arrys/OT-Thing/Firmware/src/otvalues.cpp

#include <Arduino.h>
#include "otvalues.h"
#include "otcontrol.h"
#include "mqtt.h"
#include "sensors.h"
#include "devstatus.h"

struct OTItem {
    OpenThermMessageID id;
    PGM_P name;
    static PGM_P getName(OpenThermMessageID id);
};

using enum OpenThermMessageID;

OTValueStatus* OTValue::status = nullptr;
OTValueSlaveConfigMember* OTValue::slaveConfig = nullptr;
OTValueVentSlaveConfigMember* OTValue::ventSlaveConfig = nullptr;

PGM_P KEY_MEMBERID PROGMEM = "memberId";

static const OTItem OTITEMS[] PROGMEM = {
//  ID of message                                   string id for MQTT                  
    {Status,                    PSTR("status")},
    {TSet,                      PSTR("ch_set_t")},
    {MConfigMMemberIDcode,      PSTR("master_config_member")},
    {SConfigSMemberIDcode,      PSTR("slave_config_member")},
    {RemoteRequest,             PSTR("remote_req")},
    {ASFflags,                  PSTR("fault_flags")},
    {RBPflags,                  PSTR("rp_flags")},
    {CoolingControl,            PSTR("cooling_ctrl")},
    {TsetCH2,                   PSTR("ch_set_t2")},
    {TrOverride,                PSTR("tr_override")},
    {TSP,                       PSTR("num_tsps")},
    {FHBsize,                   PSTR("size_fhb")},
    {MaxRelModLevelSetting,     PSTR("max_rel_mod")},
    {MaxCapacityMinModLevel,    PSTR("max_cap_min_mod")},
    {TrSet,                     PSTR("room_set_t")},
    {RelModLevel,               PSTR("rel_mod")},
    {CHPressure,                PSTR("ch_pressure")},
    {DHWFlowRate,               PSTR("dhw_flow_rate")},
    {DayTime,                   PSTR("day_time")},
    {Date,                      PSTR("date")},
    {Year,                      PSTR("year")},
    {TrSetCH2,                  PSTR("room_set_t2")},
    {Tr,                        PSTR("room_t")},
    {Tboiler,                   PSTR("flow_t")},
    {Tdhw,                      PSTR("dhw_t")},
    {Toutside,                  PSTR("outside_t")},
    {Tret,                      PSTR("return_t")},
    {TflowCH2,                  PSTR("flow_t2")},
    {Tdhw2,                     PSTR("dhw_t2")},
    {Texhaust,                  PSTR("exhaust_t")},
    {TboilerHeatExchanger,      PSTR("boiler_heat_ex_t")},
    {BoilerFanSpeedSetpointAndActual, PSTR("boiler_fan")},
    {FlameCurrent,              PSTR("flame_current")},
    {TrCH2,                     PSTR("room_t2")},
    {TrOverride2,               PSTR("tr_override2")},           
    {TdhwSetUBTdhwSetLB,        PSTR("dhw_bounds")},
    {MaxTSetUBMaxTSetLB,        PSTR("ch_bounds")},
    {TdhwSet,                   PSTR("dhw_set_t")},
    {MaxTSet,                   PSTR("max_set_t")},
    {StatusVentilationHeatRecovery, PSTR("vent_status")},
    {Vset,                      PSTR("rel_vent_set")},
    {ASFflagsOEMfaultCodeVentilationHeatRecovery, PSTR("vent_fault_flags")},
    {SConfigSMemberIDCodeVentilationHeatRecovery, PSTR("vent_slave_config_member")},
    {OpenThermVersionVentilationHeatRecovery,   PSTR("vent_ot_version")},
    {VentilationHeatRecoveryVersion,    PSTR("vent_prod_version")},
    {RelVentLevel,              PSTR("rel_vent")},
    {RHexhaust,                 PSTR("rel_hum_exhaust")},
    {CO2exhaust,                PSTR("co2_exhaust")},
    {Tsi,                       PSTR("supply_inlet_t")},
    {Tso,                       PSTR("supply_outlet_t")},
    {Tei,                       PSTR("exhaust_inlet_t")},
    {Teo,                       PSTR("exhaust_outlet_t")},
    {RPMexhaust,                PSTR("exhaust_fan_speed")},
    {RPMsupply,                 PSTR("supply_fan_speed")},
    {Brand,                     PSTR("brand")},
    {BrandVersion,              PSTR("brand_version")},
    {BrandSerialNumber,         PSTR("brand_serial")},
    {PowerCycles,               PSTR("power_cycles")},
    {RemoteOverrideFunction,    PSTR("remote_override_function")},
    {UnsuccessfulBurnerStarts,  PSTR("unsuccessful_burner_starts")},
    {FlameSignalTooLowNumber,   PSTR("num_flame_signal_low")},
    {OEMDiagnosticCode,         PSTR("oem_diag_code")},
    {SuccessfulBurnerStarts,    PSTR("burner_starts")},
    {CHPumpStarts,              PSTR("ch_pump_starts")},
    {DHWPumpValveStarts,        PSTR("dhw_pump_starts")},
    {DHWBurnerStarts,           PSTR("dhw_burner_starts")},
    {BurnerOperationHours,      PSTR("burner_op_hours")},
    {CHPumpOperationHours,      PSTR("chpump_op_hours")},
    {DHWPumpValveOperationHours,PSTR("dhwpump_op_hours")},
    {DHWBurnerOperationHours,   PSTR("dhw_burner_op_hours")},
    {OpenThermVersionMaster,    PSTR("master_ot_version")},
    {OpenThermVersionSlave,     PSTR("slave_ot_version")},
    {MasterVersion,             PSTR("master_prod_version")},
    {SlaveVersion,              PSTR("slave_prod_version")}
};

OTValue *slaveValues[56] = { // replydata collected (read) from a connnected slave (boiler / ventilation / solar)
    new OTValueSlaveConfigMember(),
    new OTValueVentSlaveConfigMember(),
    new OTValueProductVersion(  OpenThermVersionSlave,      0,                 PSTR("OT-version slave")),
    new OTValueProductVersion(  SlaveVersion,               0,                 PSTR("productversion slave")),
    new OTValueStatus(),
    new OTValueVentStatus(),
    new OTValueCapacityModulation(),
    new OTValueTempBounds(TdhwSetUBTdhwSetLB,                                   PSTR("DHW")),
    new OTValueTempBounds(MaxTSetUBMaxTSetLB,                                   PSTR("CH")),
    new OTValueFloatTemp(       TrOverride,                                     PSTR("room setpoint override")),
    new OTValueFloat(           RelModLevel,                10,                 PSTR("rel. modulation")),
    new OTValueFloat(           CHPressure,                 30,                 PSTR("CH pressure")),
    new OTValueFloat(           DHWFlowRate,                10,                 PSTR("flow rate")),
    new OTValueFloatTemp(       Tboiler,                                        PSTR("flow temp.")),
    new OTValueFloatTemp(       TflowCH2,                                       PSTR("flow temp. 2")),
    new OTValueFloatTemp(       Tdhw,                                           PSTR("DHW temperature")),
    new OTValueFloatTemp(       Tdhw2,                                          PSTR("DHW temperature 2")),
    new OTValueFloatTemp(       Toutside,                                       PSTR("outside temp.")),
    new OTValueFloatTemp(       Tret,                                           PSTR("return temp.")),
    new OTValuei16(             Texhaust,                   10,                 PSTR("exhaust temp.")),
    new OTValueFloatTemp(       TrOverride2,                                    PSTR("room setpoint 2 override")),
    new OTValueProductVersion(  OpenThermVersionVentilationHeatRecovery,    0,  PSTR("OT-version slave")),
    new OTValueProductVersion(  VentilationHeatRecoveryVersion,             0,  PSTR("productversion slave")),
    new OTValueu16(             RelVentLevel,               10,                 PSTR("rel. ventilation")),
    new OTValueu16(             RHexhaust,                  10,                 PSTR("humidity exhaust")),
    new OTValueu16(             CO2exhaust,                 10,                 PSTR("CO2 exhaust")),
    new OTValueFloatTemp(       Tsi,                                            PSTR("supply inlet temp.")),
    new OTValueFloatTemp(       Tso,                                            PSTR("supply outlet temp.")),
    new OTValueFloatTemp(       Tei,                                            PSTR("exhaust inlet temp.")),
    new OTValueFloatTemp(       Teo,                                            PSTR("exhaust outlet temp.")),
    new OTValueu16(             RPMexhaust,                 10,                 PSTR("exhaust fan speed")),
    new OTValueu16(             RPMsupply,                  10,                 PSTR("supply fan speed")),
    new OTValueu16(             PowerCycles,                180,                PSTR("power cycles")),
    new OTValueu16(             UnsuccessfulBurnerStarts,   60,                 PSTR("failed burnerstarts")),
    new OTValueu16(             FlameSignalTooLowNumber,    120,                PSTR("Flame sig low")),
    new OTValueu16(             OEMDiagnosticCode,          60,                 PSTR("OEM diagnostic code")),
    new OTValueu16(             SuccessfulBurnerStarts,     120,                PSTR("burnerstarts")),
    new OTValueu16(             CHPumpStarts,               60,                 PSTR("CH pump starts")),
    new OTValueu16(             DHWPumpValveStarts,         60,                 PSTR("DHW pump starts")),
    new OTValueu16(             DHWBurnerStarts,            120,                PSTR("DHW burnerstarts")),
    new OTValueOperatingHours(  BurnerOperationHours,                           PSTR("burner op. hours")),
    new OTValueOperatingHours(  CHPumpOperationHours,                           PSTR("DHW pump op. hours")),
    new OTValueOperatingHours(  DHWPumpValveOperationHours,                     PSTR("DHW pump/value op. hours")),
    new OTValueOperatingHours(  DHWBurnerOperationHours,                        PSTR("DHW op. hours")),
    new OTValueFaultFlags(                                                      30),
    new OTValueRemoteParameter(),
    new OTValueRemoteOverrideFunction(),
    new OTValueVentFaultFlags(                                                  30),
    new OTValueHeatExchangerTemp(),
    new OTValueBoilerFanSpeed(),
    new OTValueFlameCurrent(),
    new BrandInfo(              Brand,                                          PSTR("brand")),
    new BrandInfo(              BrandVersion,                                   PSTR("brand version")),
    new BrandInfo(              BrandSerialNumber,                              PSTR("brand serial")),
    new OTValueBufSize(         TSP),
    new OTValueBufSize(         FHBsize)
};


OTValue *masterValues[20] = { // requestdata sent (written) from OTthing (mode master) or connected roomunit (mode repeater)
    new OTValueFloat(           TSet,                   -1),
    new OTValueFloat(           TsetCH2,                -1),
    new OTValueFloat(           Tr,                     -1),
    new OTValueFloat(           TrCH2,                  -1),
    new OTValueFloat(           TrSet,                  -1),
    new OTValueFloat(           TrSetCH2,               -1),
    new OTValueProductVersion(  MasterVersion,          -1, PSTR("productversion master")),
    new OTValueFloat(           MaxRelModLevelSetting,  -1),
    new OTValueProductVersion(  OpenThermVersionMaster, -1, PSTR("OT-version master")),
    new OTValueMasterConfig(),
    new OTValueFloat(           TdhwSet,                -1),
    new OTValueMasterStatus(),
    new OTValueVentMasterStatus(),
    new OTValueDayTime(),
    new OTValueDate(),
    new OTValueu16(             Year,                   -1),
    new OTValueu16(             Vset,                   -1),
    new OTValueFloat(           Toutside,               -1),
    new OTValueFloat(           MaxTSet,                -1),
    new OTValueFloat(           CoolingControl,         -1),
};


OTValue *roomUnitValues[9] = { // requestdata sent (written) from a connected roomunit
    new OTValueFloatTemp(       TSet,                   PSTR("flow temp. setpoint")),
    new OTValueFloatTemp(       TsetCH2,                PSTR("flow temp. 2 setpoint")),
    new OTValueFloatTemp(       Tr,                     PSTR("room temp.")),
    new OTValueFloatTemp(       TrCH2,                  PSTR("room temp. 2")),
    new OTValueFloatTemp(       TrSet,                  PSTR("room temp. setpoint")),
    new OTValueFloatTemp(       TrSetCH2,               PSTR("room temp. 2 setpoint")),
    new OTValueFloatTemp(       TdhwSet,                PSTR("DHW setpoint")),
    new OTValueMasterStatus(),
    new OTValueVentMasterStatus(),
};

const char* getOTname(OpenThermMessageID id) {
    return OTItem::getName(id);
}

PGM_P OTItem::getName(OpenThermMessageID id) {
    for (int i=0; i<sizeof(OTITEMS) / sizeof(OTITEMS[0]); i++)
        if (OTITEMS[i].id == id)
            return OTITEMS[i].name;
    return nullptr;
}

/**
 * @param interval -1: never query. 0: only query once. >0: query every interval seconds
 */
OTValue::OTValue(const OpenThermMessageID id, const int interval, PGM_P haName):
        interval(interval),
        id(id),
        value(0),
        enabled(interval != -1),
        discFlag(false),
        setFlag(false),
        numSet(0),
        lastMsgResult(OpenThermMessageType::RESERVED),
        haName(haName),
        entityCategory(nullptr) {
}

OTValue* OTValue::getSlaveValue(const OpenThermMessageID id) {
    for (auto *val: slaveValues) {
        if (val->id == id)
            return val;
    }
    return nullptr;
}

OTValue* OTValue::getMasterValue(const OpenThermMessageID id) {
    for (auto *val: masterValues) {
        if (val->id == id)
            return val;
    }
    return nullptr;
}

OTValue* OTValue::getroomUnitValue(const OpenThermMessageID id) {
    for (auto *val: roomUnitValues) {
        if (val->id == id)
            return val;
    }
    return nullptr;
}

void OTValue::setTexhaustAsFloat(const bool asFloat) {
    static bool current = false;
    if (asFloat == current)
        return;
    current = asFloat;
    for (auto *&val: slaveValues) {
        if (val->id == Texhaust) {
            delete val;
            val = asFloat
                ? (OTValue*) new OTValueFloatTemp(Texhaust,      PSTR("exhaust temp."))
                : (OTValue*) new OTValuei16(      Texhaust, 10,  PSTR("exhaust temp."));
            return;
        }
    }
}

bool OTValue::process() {
    if (!enabled || (interval == -1))
        return false;

    if (isSet() && (interval == 0))
        return false;

    if ((lastTransfer > 0) && ((millis() - lastTransfer) / 1000 < interval))
        return false;

    unsigned long request = OpenTherm::buildRequest(OpenThermMessageType::READ_DATA, id, value);
    otcontrol.sendRequest('T', request);
    lastTransfer = millis();
    return true;
}

OpenThermMessageID OTValue::getId() const {
    return id;
}

bool OTValue::isSet() const {
    return setFlag;
}

bool OTValue::hasReply() const {
    return numSet > 0;
}

OpenThermMessageType OTValue::getLastMsgResult() const {
    return lastMsgResult;
}

bool OTValue::sendDiscovery() {
    const char *name = getName();
    if (name == nullptr)
        return false;

    String sName = FPSTR(name);
    String sHaName;

    if (haName != nullptr)
        sHaName = FPSTR(haName);

    if (isRoomunitValue()) {
        sName += F("_ru");
        sHaName += F(" roomunit");
    }
    
/* missing discoveries: 
    {OpenThermMessageID::DayTime,                   PSTR("day_time")},
    {OpenThermMessageID::Date,                      PSTR("date")},
    {OpenThermMessageID::Year,                      PSTR("year")},
    {OpenThermMessageID::Vset,                      PSTR("rel_vent_set")},
    {OpenThermMessageID::RemoteOverrideFunction,    PSTR("remote_override_function")},
*/
    if (haName != nullptr) {
        haDisc.createSensor(sHaName, sName);
    }

    switch (id) {
    case CO2exhaust:
        haDisc.setUnit(FPSTR(HA_UNIT_PPM));
        haDisc.setDeviceClass(FPSTR(HA_DEVICE_CLASS_CARBON_DIOXIDE));
        break;

    case RelModLevel:
        haDisc.createPowerFactorSensor(sHaName, sName);
        break;

    case CHPressure:
        haDisc.createPressureSensor(sHaName, sName);
        break;

    case RelVentLevel:
        break;

    case RHexhaust:
        haDisc.setDeviceClass(FPSTR(HA_DEVICE_CLASS_HUMIDITY));
        haDisc.setUnit(FPSTR(HA_UNIT_PERCENT));
        break;

    case RPMexhaust:
        haDisc.setUnit(FPSTR(HA_UNIT_RPM));
        break;

    case RPMsupply:
        haDisc.setUnit(FPSTR(HA_UNIT_RPM));
        break;

    case TSet:
        haDisc.createTempSensor(F("flow set temp."), sName);
        break;

    case Texhaust:
        haDisc.createTempSensor(sHaName, sName);
        break;

    case DHWFlowRate:
        haDisc.setUnit(FPSTR(HA_UNIT_L_MIN));
        haDisc.setDeviceClass(FPSTR(HA_DEVICE_CLASS_VOLUME_FLOW_RATE));
        break;

    default:
        if (haName == nullptr)
            return false;
    }

    return sendDiscovery("");
}

bool OTValue::isSlaveValue() const {
    for (auto *valobj: slaveValues) {
        if (valobj == this)
            return true;
    }
    return false;
}

bool OTValue::isMasterValue() const {
    for (auto *valobj: masterValues) {
        if (valobj == this) {
            return true;
        }
    }
    return false;
}

bool OTValue::isRoomunitValue() const {
    for (auto *valobj: roomUnitValues) {
        if (valobj == this)
            return true;
    }
    return false;
}

bool OTValue::sendDiscovery(String field) {
    String fn = FPSTR(getName());
    if (!field.isEmpty()) {
        fn += '.';
        fn += field;
    }
    
    String valTmpl;

    if (isSlaveValue())
        valTmpl = mqtt.getValueTemplate(Mqtt::VALTMPL_SLAVE, fn.c_str());
    else if (isMasterValue())
        valTmpl = mqtt.getValueTemplate(Mqtt::VALTMPL_MASTER, fn.c_str());
    else if (isRoomunitValue())
        valTmpl = mqtt.getValueTemplate(Mqtt::VALTMPL_ROOMUNIT, fn.c_str());

    if (valTmpl.isEmpty())
        return haDisc.publish(false);    

    if (interval == 0)
        haDisc.setStateClass("");

    haDisc.setValueTemplate(valTmpl);
    return haDisc.publish(enabled);
}

void OTValue::refreshDisc() {
    discFlag = false;
    if (isSet() && enabled)
        discFlag = sendDiscovery();
}

const char* OTValue::getName() const {
    return OTItem::getName(id);
}

bool OTValue::isDataMessage(const OpenThermMessageID id, const OpenThermMessageType ty) {
    return (ty == OpenThermMessageType::READ_ACK) 
        || (ty == OpenThermMessageType::WRITE_DATA)
        || (id == OpenThermMessageID::Status)
        || (id == OpenThermMessageID::StatusSolarStorage)
        || (id == OpenThermMessageID::StatusVentilationHeatRecovery);
}

void OTValue::setValue(const OpenThermMessageType ty, const uint16_t val) {
    numSet++;
    
    if (isDataMessage(id, ty)) {
        value = val;
        setFlag = true;
        enabled = true;
    }
    else
        enabled = false;

    if (!discFlag)
        discFlag = sendDiscovery();

    // only save msgresult when message is a reply
    if ( (ty != OpenThermMessageType::WRITE) && (ty != OpenThermMessageType::READ) )
        lastMsgResult = ty;
}

void OTValue::setMsgResult(const OpenThermMessageType ty) {
    lastMsgResult = ty;
}

uint16_t OTValue::getValue() {
    return value;
}

void OTValue::init(const bool enabled) {
    this->enabled = enabled;
    numSet = 0;
    setFlag = false;
}

void OTValue::unset() {
    setFlag = false;
}

void OTValue::getJson(JsonObject &obj, const bool addResult) const {
    if (enabled) {
        JsonVariant var = obj[FPSTR(getName())].to<JsonVariant>();
        if (!isSet()) {
            var.set(nullptr);
            return;
        }

        if (addResult) {
            var[F("result")] = (lastMsgResult == OpenThermMessageType::WRITE_ACK) || (lastMsgResult == OpenThermMessageType::READ_ACK);
            var = var[F("data")].to<JsonVariant>();
        }
        getValue(var);   
    }
}

void OTValue::getStatus(JsonObject &obj) const {
    JsonObject stat = obj[FPSTR(getName())].to<JsonObject>();

    stat[F("id")] = (int) id;
    stat[F("enabled")] = enabled;
    stat[F("lastMsgResult")] = (int) lastMsgResult;
    stat[F("numSet")] = numSet;
    if (isSet()) {
        stat[F("value")] = String(value, HEX);
        stat[F("disc")] = discFlag;
    }
}

OTValueu16::OTValueu16(const OpenThermMessageID id, const int interval, PGM_P haName):
        OTValue(id, interval, haName) {
}

void OTValueu16::getValue(JsonVariant var) const {
    var.set<unsigned int>(value);
}


OTValueBufSize::OTValueBufSize(const OpenThermMessageID id):
        OTValue(id, 0) {
}

void OTValueBufSize::getValue(JsonVariant var) const {
    var.set<unsigned int>(value >> 8);
}


OTValueOperatingHours::OTValueOperatingHours(const OpenThermMessageID id, PGM_P haName):
        OTValueu16(id, 300, haName) {
}

bool OTValueOperatingHours::sendDiscovery() {
    haDisc.createHourDuration(FPSTR(haName), FPSTR(getName()));
    return OTValue::sendDiscovery("");
}


OTValuei16::OTValuei16(const OpenThermMessageID id, const int interval, PGM_P haName):
        OTValue(id, interval, haName) {
}

void OTValuei16::getValue(JsonVariant var) const {
    var.set<int>(value);
}


OTValueFloat::OTValueFloat(const OpenThermMessageID id, const int interval, PGM_P haName):
        OTValue(id, interval, haName) {
}

void OTValueFloat::getValue(JsonVariant var) const {
    double d = round((int16_t)value * 10 / 256.0) / 10.0;
    var.set<double>(d);
}


OTValueFloatTemp::OTValueFloatTemp(const OpenThermMessageID id, PGM_P haName):
        OTValueFloat(id, 10, haName) {
}

bool OTValueFloatTemp::sendDiscovery() {
    String sName = FPSTR(haName);
    String sId = FPSTR(getName());

    if (isRoomunitValue()) {
        sId += F("_ru");
        sName += F(" roomunit");
    }

    haDisc.createTempSensor(sName, sId);
    return OTValue::sendDiscovery("");
}


OTValueFlags::OTValueFlags(const OpenThermMessageID id, const int interval, const Flag *flagtable, const uint8_t numFlags):
        OTValue(id, interval),
        numFlags(numFlags),
        flagTable(flagtable) {
}

void OTValueFlags::getValue(JsonVariant var) const {
    var[F("value")] = String(value, HEX);
    for (uint8_t i=0; i<numFlags; i++)
        var[FPSTR(flagTable[i].field)] = (bool) (value & (1<<flagTable[i].bit));
}

bool OTValueFlags::sendDiscFlag(const Flag *flag, const bool enb)  {
    if (flag->discName == nullptr)
        return true;

    String sName = flag->discName;
    String sId = FPSTR(flag->field);

    if (isRoomunitValue()) {
        sName += F(" RU");
        sId += F("_ru");
    }

    String dc;
    if (flag->haDevClass != nullptr)
        dc = FPSTR(flag->haDevClass);

    haDisc.createBinarySensor(sName, sId, dc);
    String fn = getName();
    fn += '.';
    fn += FPSTR(flag->field);

    String valTmpl;

    if (isSlaveValue())
        valTmpl = mqtt.getValueTemplateBool(Mqtt::VALTMPL_SLAVE, fn.c_str());
    else if (isMasterValue())
        valTmpl = mqtt.getValueTemplateBool(Mqtt::VALTMPL_MASTER, fn.c_str());
    else if (isRoomunitValue())
        valTmpl = mqtt.getValueTemplateBool(Mqtt::VALTMPL_ROOMUNIT, fn.c_str());

    haDisc.setValueTemplate(valTmpl);
    haDisc.setEntityCategory(entityCategory);
    return haDisc.publish(enb);
};

bool OTValueFlags::sendDiscovery() {
    for (uint8_t i=0; i<numFlags; i++) {
        if (!sendDiscFlag(&flagTable[i], enabled))
            return false;
    }
    return true;
}


OTValueStatus::OTValueStatus():
        OTValueFlags(Status, -1, flags, sizeof(flags) / sizeof(flags[0])) {
    OTValue::status = this;
}

bool OTValueStatus::getChActive(const uint8_t channel) const{
    return isSet() ? ((value & (1<<((channel == 0) ? BIT_CH_MODE : BIT_CH2_MODE))) != 0) : false;
}

bool OTValueStatus::getFlame() const {
    return isSet() ? ((value & (1<<BIT_FLAME)) != 0) : false;
}

bool OTValueStatus::getDhwActive() const {
    return isSet() ? ((value & (1<<BIT_DHW_MODE)) != 0) : false;
}

bool OTValueStatus::getCoolingActive() const {
    return isSet() ? ((value & (1<<BIT_COOLING)) != 0) : false;
}

void OTValueStatus::getValue(JsonVariant var) const {
    OTValueFlags::getValue(var);

    if (slaveConfig->isSet()) {
        if (!slaveConfig->hasDHW())
            var.remove(PSTR(DHW_MODE));

        if (!slaveConfig->hasCh(1))
            var.remove(PSTR(CH2_MODE));

        if (!slaveConfig->hasCooling())
            var.remove(PSTR(COOLING));
    }
}

bool OTValueStatus::sendDiscovery() {
    if (!slaveConfig->isSet())
        return false;

    for (uint8_t i=0; i<numFlags; i++) {
        bool enb = enabled;
        switch (flagTable[i].bit){
        case BIT_CH2_MODE:
            enb &= slaveConfig->hasCh(1);
            break;

        case BIT_DHW_MODE:
            enb &= slaveConfig->hasDHW();
            break;

        case BIT_COOLING:
            enb &= slaveConfig->hasCooling();
            break;

        default:
            break;
        }
        
        if (!sendDiscFlag(&flagTable[i], enb))
            return false;
    }
    return true;
}


OTValueMasterStatus::OTValueMasterStatus():
        OTValueFlags(Status, -1, flags, sizeof(flags) / sizeof(flags[0])) {
}

bool OTValueMasterStatus::sendDiscovery() {
    for (uint8_t i=0; i<numFlags; i++) {
        bool enb = enabled;
        switch (flagTable[i].bit) {
        case BIT_DHW_ENABLE:
            enb &= slaveConfig->hasDHW();
            break;

        case BIT_COOLING_ENABLE:
            enb &= slaveConfig->hasCooling();
            break;

        case BIT_CH2_ENABLE:
            enb &= slaveConfig->hasCh(1);
            break;

        case BIT_DHW_BLOCKING:
            enb &= slaveConfig->hasDHW();
            break;

        default:
            break;
        }

        if (!sendDiscFlag(&flagTable[i], enb))
            return false;
    }
    return true;
}

void OTValueMasterStatus::getValue(JsonVariant var) const {
    OTValueFlags::getValue(var);

    if (slaveConfig->isSet()) {
        if (!slaveConfig->hasDHW())
            var.remove(PSTR(DHW_ENABLE));

        if (!slaveConfig->hasCh(1))
            var.remove(PSTR(CH2_ENABLE));

        if (!slaveConfig->hasCooling())
            var.remove(PSTR(COOLING_ENABLE));
    }
}


OTValueVentStatus::OTValueVentStatus():
        OTValueFlags(StatusVentilationHeatRecovery, -1, flags, sizeof(flags) / sizeof(flags[0])) {
}


OTValueVentMasterStatus::OTValueVentMasterStatus():
        OTValueFlags(StatusVentilationHeatRecovery, -1, flags, sizeof(flags) / sizeof(flags[0])) {
}

bool OTValueVentMasterStatus::sendDiscovery() {
    return true;
}

OTValueSlaveConfigMember::OTValueSlaveConfigMember():
        OTValueFlags(SConfigSMemberIDcode, 0, flags, sizeof(flags) / sizeof(flags[0])) {
    entityCategory = HA_ENTITY_CATEGORY_DIAGNOSTIC;
    slaveConfig = this;
}

void OTValueSlaveConfigMember::getValue(JsonVariant var) const {
    OTValueFlags::getValue(var);
    var[FPSTR(KEY_MEMBERID)] = value & 0xFF;
}

bool OTValueSlaveConfigMember::hasDHW() const {
    return (value & (1<<8)) != 0;
}

bool OTValueSlaveConfigMember::hasCh(const uint8_t ch) const {
    if (ch == 1)
        return (value & (1<<13)) != 0;
    else
        return true;
}

bool OTValueSlaveConfigMember::hasCooling() const {
    return (value & (1<<10)) != 0;
}

bool OTValueSlaveConfigMember::sendDiscovery() {
    haDisc.createSensor(F("slave member ID"), F("slave_member_id"));
    if (!OTValue::sendDiscovery(FPSTR(KEY_MEMBERID)))
        return false;

    if (!OTValueFlags::sendDiscovery())
        return false;
    if (!otcontrol.sendCapDiscoveries())
        return false;
    return true;
}


OTValueVentSlaveConfigMember::OTValueVentSlaveConfigMember():
        OTValueFlags(SConfigSMemberIDCodeVentilationHeatRecovery, 0, flags, sizeof(flags) / sizeof(flags[0])) {
    entityCategory = HA_ENTITY_CATEGORY_DIAGNOSTIC;
    ventSlaveConfig = this;
}

void OTValueVentSlaveConfigMember::getValue(JsonVariant var) const {
    OTValueFlags::getValue(var);
    var[FPSTR(KEY_MEMBERID)] = value & 0xFF;
}

bool OTValueVentSlaveConfigMember::sendDiscovery() {
    haDisc.createSensor(F("vent member ID"), F("vent_member_id"));
    if (!OTValue::sendDiscovery(FPSTR(KEY_MEMBERID)))
        return false;

    if (!OTValueFlags::sendDiscovery())
        return false;

    if (!otcontrol.ventCtrl.sendCapDiscoveries())
        return false;

    return true;
}

bool OTValueVentSlaveConfigMember::isHeatRecovery() const {
    return (value & (1<<8)) != 0;
}

bool OTValueVentSlaveConfigMember::hasBypass() const {
    return (value & (1<<9)) != 0;
}

bool OTValueVentSlaveConfigMember::hasVarSpeedControl() const {
    return (value & (1<<10)) != 0;
}


OTValueFaultFlags::OTValueFaultFlags(const int interval):
        OTValueFlags(ASFflags, interval, flags, sizeof(flags) / sizeof(flags[0])) {
}

void OTValueFaultFlags::getValue(JsonVariant var) const {
    OTValueFlags::getValue(var);
    var[PSTR(OEM_FAULT_CODE)] = value & 0xFF;
}

bool OTValueFaultFlags::sendDiscovery() {
    if (!OTValueFlags::sendDiscovery())
        return false;

    haDisc.createSensor(F("OEM fault code"), FPSTR(OEM_FAULT_CODE));
    return OTValue::sendDiscovery(FPSTR(OEM_FAULT_CODE));
}


OTValueVentFaultFlags::OTValueVentFaultFlags(const int interval):
        OTValueFlags(ASFflagsOEMfaultCodeVentilationHeatRecovery, interval, flags, sizeof(flags) / sizeof(flags[0])) {
}

void OTValueVentFaultFlags::getValue(JsonVariant var) const {
    OTValueFlags::getValue(var);
    var[PSTR(OEM_VENT_FAULT_CODE)] = value & 0xFF;
}

bool OTValueVentFaultFlags::sendDiscovery() {
    if (!OTValueFlags::sendDiscovery())
        return false;

    haDisc.createSensor(F("OEM fault code"), FPSTR(OEM_VENT_FAULT_CODE));
    return OTValue::sendDiscovery(FPSTR(OEM_VENT_FAULT_CODE));
}


OTValueProductVersion::OTValueProductVersion(const OpenThermMessageID id, const int interval, PGM_P haName):
        OTValue(id, interval, haName) {
    entityCategory = HA_ENTITY_CATEGORY_DIAGNOSTIC;
}

bool OTValueProductVersion::sendDiscovery() {
    haDisc.createSensor(FPSTR(haName), FPSTR(getName()));
    haDisc.setStateClass("");
    return OTValue::sendDiscovery("");
}

void OTValueProductVersion::getValue(JsonVariant var) const {
    String v = String(value >> 8);
    v += '.';
    v += String(value & 0xFF);
    var.set<String>(v);
}


OTValueCapacityModulation::OTValueCapacityModulation():
        OTValue(MaxCapacityMinModLevel, 0) {
}

bool OTValueCapacityModulation::sendDiscovery() {
    haDisc.createSensor(F("Max. capacity"), FPSTR(MAX_CAPACITY));
    haDisc.setDeviceClass(F("power"));
    haDisc.setUnit(F("kW"));
    if (!OTValue::sendDiscovery(FPSTR(MAX_CAPACITY)))
        return false;
    haDisc.createSensor(F("Min. modulation"), FPSTR(MIN_MODULATION));
    haDisc.setUnit(FPSTR(HA_UNIT_PERCENT));
    return OTValue::sendDiscovery(FPSTR(MIN_MODULATION));
}

void OTValueCapacityModulation::getValue(JsonVariant var) const {
    var[PSTR(MAX_CAPACITY)] = value >> 8;
    var[PSTR(MIN_MODULATION)] = value & 0xFF;
}

OTValueTempBounds::OTValueTempBounds(const OpenThermMessageID id, const char *namePrefix):
        OTValue(id, 0),
        namePrefix(namePrefix) {
}

void OTValueTempBounds::getValue(JsonVariant var) const {
    var[PSTR(MAX)] = value >> 8;
    var[PSTR(MIN)] = value & 0xFF;
}

bool OTValueTempBounds::sendDiscovery() {
    String name = FPSTR(namePrefix);
    name += F(" max. temp.");
    String id = FPSTR(namePrefix);
    id += F("_max");
    haDisc.createTempSensor(name, id);
    if (!OTValue::sendDiscovery(FPSTR(MAX)))
        return false;

    name = FPSTR(namePrefix);
    name += F(" min. temp.");
    id = FPSTR(namePrefix);
    id += F("_min");
    haDisc.createTempSensor(name, id);
    return OTValue::sendDiscovery(FPSTR(MIN));
}


OTValueMasterConfig::OTValueMasterConfig():
        OTValueFlags(MConfigMMemberIDcode, -1, flags, sizeof(flags) / sizeof(flags[0])) {
}

void OTValueMasterConfig::getValue(JsonVariant var) const {
    OTValueFlags::getValue(var);
    var[FPSTR(KEY_MEMBERID)] = value & 0xFF;
}

bool OTValueMasterConfig::sendDiscovery() {
    return true;
}

OTValueRemoteParameter::OTValueRemoteParameter():
        OTValueFlags(RBPflags, 0, flags, sizeof(flags) / sizeof(flags[0])) {
}


OTValueRemoteOverrideFunction::OTValueRemoteOverrideFunction():
        OTValueFlags(RemoteOverrideFunction, 0, flags, sizeof(flags) / sizeof(flags[0])) {
}

bool OTValueRemoteOverrideFunction::sendDiscovery() {
    return true;
}

OTValueDayTime::OTValueDayTime():
        OTValue(DayTime, 0) {
}

void OTValueDayTime::getValue(JsonVariant var) const {
    var[F("dayOfWeek")] = (value >> 13) & 0x07;
    var[F("hour")] = (value >> 8) & 0x1F;
    var[F("minute")] = value & 0xFF;
}

bool OTValueDayTime::sendDiscovery() {
    return true;
}


OTValueDate::OTValueDate():
        OTValue(Date, 0) {
}

void OTValueDate::getValue(JsonVariant var) const {
    var[F("month")] = (value >> 8);
    var[F("day")] = value & 0xFF;
}

bool OTValueDate::sendDiscovery() {
    return true;
}


OTValueHeatExchangerTemp::OTValueHeatExchangerTemp():
        OTValueFloat(TboilerHeatExchanger, 30) {
}

bool OTValueHeatExchangerTemp::sendDiscovery() {
    haDisc.createTempSensor(F("Heat exchange temp."), FPSTR(getName()));
    return OTValue::sendDiscovery("");
}


OTValueBoilerFanSpeed::OTValueBoilerFanSpeed():
        OTValue(BoilerFanSpeedSetpointAndActual, 30) {
}

void OTValueBoilerFanSpeed::getValue(JsonVariant var) const {
    var[PSTR(SETPOINT)] = value >> 8;
    var[PSTR(ACTUAL)] = value & 0xFF;
}

bool OTValueBoilerFanSpeed::sendDiscovery() {
    haDisc.createSensor(F("Boiler fan speed setpoint"), FPSTR(SETPOINT));
    haDisc.setUnit(FPSTR(HA_UNIT_HZ));
    String field = FPSTR(getName());
    if (!OTValue::sendDiscovery(FPSTR(SETPOINT)))
        return false;
    
    haDisc.createSensor(F("Boiler fan speed actual"), FPSTR(ACTUAL));
    haDisc.setUnit(FPSTR(HA_UNIT_HZ));
    return OTValue::sendDiscovery(FPSTR(ACTUAL));
}


OTValueFlameCurrent::OTValueFlameCurrent():
        OTValueFloat(FlameCurrent, 30, PSTR("Flame current")) {
}

bool OTValueFlameCurrent::sendDiscovery() {
    haDisc.createSensor(FPSTR(haName), FPSTR(getName()));
    haDisc.setUnit(F("μA"));
    haDisc.setDeviceClass(FPSTR(HA_DEVICE_CLASS_CURRENT));
    return OTValue::sendDiscovery("");
}


BrandInfo::BrandInfo(const OpenThermMessageID id, const char *name):
        OTValue(id, 0, name) {
    buf[0] = 0;
}

void BrandInfo::init(const bool enabled) {
    OTValue::init(enabled);
    buf[0] = 0;
}

bool BrandInfo::process() {
    if (isSet() || !enabled) 
        return false;

    unsigned long req = OpenTherm::buildRequest(OpenThermMessageType::READ_DATA, id, strlen(buf) << 8);
    otcontrol.sendRequest('T', req);
    return true;
}

void BrandInfo::setValue(const OpenThermMessageType ty, const uint16_t val) {
    lastMsgResult = ty;
    numSet++;

    if (ty == OpenThermMessageType::READ_ACK) {
        value = val;
        if (strlen(buf) >= sizeof(buf) - 1) {
            setFlag = true;
            return;
        }
        buf[strlen(buf) + 1] = 0;
        buf[strlen(buf)] = val & 0xFF;
        if ( (strlen(buf) == (val >> 8)) || ((val & 0xFF) == 0) )
            setFlag = true;
    }
    else {
        setFlag = (strlen(buf) > 0);
        enabled = setFlag;
    }

    if ((isSet() || !enabled) && !discFlag)
        discFlag = sendDiscovery();
}

void BrandInfo::getValue(JsonVariant var) const {
    var.set<String>(buf);
}
