arrys/OT-Thing/Firmware/helper.py

import gzip
import os
import subprocess
import sys

try:
    Import("env")  # type: ignore[name-defined]
    SOURCE_HTML = os.path.join(env["PROJECT_DATA_DIR"], "index.html")
    TARGET_HTML = os.path.join(env["PROJECT_DIR"], "include/html.h")
    REQUIREMENTS_FILE = os.path.join(env["PROJECT_DIR"], "requirements.txt")
except NameError:
    env = None
    REQUIREMENTS_FILE = os.path.join(os.getcwd(), "requirements.txt")

def ensure_requirements_installed():
    if not os.path.exists(REQUIREMENTS_FILE):
        return
    try:
        subprocess.check_call([
            sys.executable, "-m", "pip", "install", "-q", "-r", REQUIREMENTS_FILE
        ])
    except Exception as install_err:
        print(f"\033[91mFailed to auto-install requirements.txt: {install_err}\033[0m")

try:
    import minify_html
except ImportError:
    minify_html = None
    ensure_requirements_installed()
    try:
        import minify_html
    except ImportError as import_err:
        print(f"\033[91mminify_html still unavailable after install attempt: {import_err}\033[0m")

platform = env.PioPlatform()
board = env.BoardConfig()
mcu = board.get("build.mcu", "esp32")  # works for ESP8266 and ESP32

def copy_html(env):
    print("Creating html.h from index.html")
    with open(SOURCE_HTML, "r", encoding="utf-8") as fin:
        content = fin.read()
        if env["PIOENV"] in ("release", "production") and minify_html is not None:
            print("minify html")
            content = minify_html.minify(
                content,
                # --- JS / CSS ---
                minify_js=True,               # minify inline <script> content
                minify_css=True,              # minify inline <style> and style= attributes
                minify_doctype=True,         # shorten <!DOCTYPE html> to <!doctype html>
                # --- Attributes ---
                keep_input_type_text_attr=True,              # keep type="text" on <input> (default is removed as redundant)
                allow_noncompliant_unquoted_attribute_values=False,  # allow unquoted attribute values (faster, but non-standard)
                allow_removing_spaces_between_attributes=False,      # remove spaces between attributes (non-standard)
                # --- Tags ---
                keep_closing_tags=False,                # keep optional closing tags e.g. </li>, </td>
                keep_html_and_head_opening_tags=False,  # keep <html> and <head> opening tags (removed when optional)
                # --- Comments ---
                keep_comments=False,          # keep regular HTML comments
                keep_ssi_comments=False,      # keep SSI comments <!--# ... -->
                remove_bangs=False,           # remove <!...> declarations (e.g. <!DOCTYPE>)
                remove_processing_instructions=True,   # strip <?...?> prologs (invalid in HTML)
                # --- Entities ---
                allow_optimal_entities=False, # use shortest entity representation (may change semantics in edge cases)
                # --- Template syntax preservation ---
                preserve_brace_template_syntax=False,          # preserve {{ }}, {% %}, {# #} (Jinja, Handlebars, etc.)
                preserve_chevron_percent_template_syntax=False, # preserve <% %> (EJS, ERB, JSP, etc.)
            )
        elif env["PIOENV"] in ("release", "production"):
            # helper.py runs inside PlatformIO's own interpreter, not the
            # project venv, so `pip install -r requirements.txt` does not
            # provide minify-html here. Shipping an unminified image silently
            # wastes flash on every unit, so fail loudly instead.
            print(f"\033[91mminify_html not installed in {sys.executable}\033[0m")
            print("\033[91mRelease builds require minify-html. Install with:\033[0m")
            print(f"\033[91m  {sys.executable} -m pip install minify-html\033[0m")
            raise RuntimeError("minify-html is required for release/production builds")

        # mtime=0 keeps the output byte-identical for identical input. Without it
        # gzip embeds the current time, so every build regenerates a different
        # html.h, forcing a recompile of portal.cpp and making release binaries
        # non-reproducible.
        compressed = gzip.compress(content.encode("utf-8"), compresslevel=9, mtime=0)
        print(f"embed html: {len(content.encode('utf-8'))} bytes raw, {len(compressed)} bytes gzip")

        with open(TARGET_HTML, "w", encoding="utf-8") as fout:
            fout.write("#pragma once\n")
            fout.write("#include <pgmspace.h>\n\n")
            fout.write(f"const size_t html_gz_len = {len(compressed)};\n")
            fout.write("const uint8_t html_gz[] PROGMEM = {\n")

            for index in range(0, len(compressed), 16):
                chunk = compressed[index:index + 16]
                fout.write("    ")
                fout.write(", ".join(f"0x{byte:02x}" for byte in chunk))
                if index + 16 < len(compressed):
                    fout.write(",")
                fout.write("\n")

            fout.write("};\n")
            
def post_build(source, target, env):
    print("Version: " + env.GetProjectOption("custom_version"))
    print("project dir: " + env["PROJECT_DIR"])
    print("build: " + env["BUILD_DIR"])

def before_upload(source, target, env):
    if env.get("UPLOAD_PORT") is not None:
        print("Using manually specified upload port:", env.get("UPLOAD_PORT"))
        return

    from serial.tools import list_ports
    
    TARGET_USB_VID = 0x303A
    TARGET_USB_PID = 0x1001

    # Try to detect device by VID/PID
    for d in list_ports.comports():
        if (d.vid == TARGET_USB_VID) and (d.pid == TARGET_USB_PID):
            print(f"Detected OTthing device on port {d.device}")
            env.Replace(UPLOAD_PORT=d.device)
            return

if env is not None:
    source_mtime = os.path.getmtime(SOURCE_HTML)
    target_mtime = 0
    if os.path.exists(TARGET_HTML):
        target_mtime = os.path.getmtime(TARGET_HTML)

    if source_mtime > target_mtime:
        print("index.html has changed; regenerating html.h")
        copy_html(env)
        
    env.AddPreAction("upload", before_upload)
    env.AddPostAction("buildprog", post_build)
