arrys/OT-Thing/Firmware/src/devstatus.cpp

#include "devstatus.h"
#include <WiFi.h>
#include <rom/rtc.h>
#include "mqtt.h"
#include "otcontrol.h"
#include "sensors.h"
#include "auxInput.h"
#include <NimBLEDevice.h>

PGM_P STR_STATKEY_MASTER PROGMEM = "master";
PGM_P STR_STATKEY_SLAVE PROGMEM = "slave";
PGM_P STR_STATKEY_ROOMUNIT PROGMEM = "roomunit";
PGM_P STR_STATKEY_ROOMCOMPINTEGRATOR PROGMEM = "roomcompInteg";
PGM_P STR_STATKEY_ROOMTEMP PROGMEM = "roomtemp";
PGM_P STR_STATKEY_ROOMSETPOINT PROGMEM = "roomsetpoint";
PGM_P STR_STATKEY_CTRLMODE PROGMEM = "ctrlMode";
PGM_P STR_STATKEY_FLOWMIN PROGMEM = "flowMin";
PGM_P STR_STATKEY_OVERRIDE_TEMP PROGMEM = "ovrdTemp";
PGM_P STR_STATKEY_OVERRIDE_ON PROGMEM = "ovrdOn";
PGM_P STR_STATKEY_OVERRIDE PROGMEM = "ovrd";
PGM_P STR_STATKEY_ACTION PROGMEM = "action";
PGM_P STR_STATKEY_DHW PROGMEM = "dhw";
PGM_P STR_STATKEY_VENT PROGMEM = "vent";
PGM_P STR_STATKEY_RETURNLIMITINTEGRATOR PROGMEM = "retLimitInteg";
PGM_P STR_STATKEY_ROOMACTION PROGMEM = "roomAction";
PGM_P STR_STATKEY_ROOMMODE PROGMEM = "roomMode";
PGM_P STR_STATKEY_SUSPENDED PROGMEM = "suspended";
PGM_P STR_STATKEY_SUMMERMODE PROGMEM = "summerMode";
PGM_P STR_STATKEY_DHWBLOCKING PROGMEM = "dhwBlocking";
PGM_P STR_STATKEY_SETPOINT PROGMEM = "setpoint";
PGM_P STR_STATKEY_COOLING PROGMEM = "cooling";
PGM_P STR_STATKEY_FLOWSETPOINT PROGMEM = "flowsetpoint";
PGM_P STR_STATKEY_ENABLE PROGMEM = "enable";
PGM_P STR_STATKEY_OPENBYPASS PROGMEM = "openBypass";
PGM_P STR_STATKEY_AUTOBYPASS PROGMEM = "autoBypass";
PGM_P STR_STATKEY_FREEVENTENABLE PROGMEM = "freeVentEnable";
PGM_P STR_STATKEY_LASTSETPOINTSRC PROGMEM = "lastSetpointSrc";
PGM_P STR_STATKEY_BYPASS PROGMEM = "bypass";
PGM_P STR_STATKEY_TXCOUNT PROGMEM = "txCount";
PGM_P STR_STATKEY_RXCOUNT PROGMEM = "rxCount";

PGM_P STR_STATKEY_FLAMESTATS PROGMEM = "flameStats";
PGM_P STR_STATKEY_FLAMESTATS_DUTY PROGMEM = "duty";
PGM_P STR_STATKEY_FLAMESTATS_FREQ PROGMEM = "freq";
PGM_P STR_STATKEY_FLAMESTATS_ONTIME PROGMEM = "onTime";
PGM_P STR_STATKEY_FLAMESTATS_OFFTIME PROGMEM = "offTime";
PGM_P STR_STATKEY_FLAMESTATS_CURRENTONTIME PROGMEM = "currentOnTime";
PGM_P STR_STATKEY_FLAMESTATS_LASTONTIME PROGMEM = "lastOnTime";

DevStatus devstatus;

class DevStatusLock: public SemHelper {
public:
    DevStatusLock(): SemHelper(devstatus.mutex, 100) {
    }
};

DevStatus::DevStatus():
        numWifiDiscon(0) {
    mutex = xSemaphoreCreateMutex();
}

bool DevStatus::lock() {
    const auto res = xSemaphoreTake(mutex, (TickType_t) 500 / portTICK_PERIOD_MS);
    return (res == pdTRUE);
}

void DevStatus::unlock() {
    xSemaphoreGive(mutex);
}

 void DevStatus::buildDoc(JsonObject doc) {
    doc[F("runtime")] = millis() / 1000UL;
    doc[F("freeHeap")] = ESP.getFreeHeap();
    doc[F("largestBlock")] = heap_caps_get_largest_free_block(MALLOC_CAP_8BIT);
    doc[F("resetInfo")] = rtc_get_reset_reason(0);
    doc[F("fw_version")] = F(BUILD_VERSION);
    doc[F("USB_connected")] = Serial.isConnected();
    doc[F("reset_reason0")] = rtc_get_reset_reason(0);
    doc[F("numWifiDisc")] = numWifiDiscon;

    struct tm timeinfo;
    if (getLocalTime(&timeinfo, 0)) {
        char buffer[64];
        strftime(buffer, sizeof(buffer), "%d.%m.%Y %H:%M:%S", &timeinfo);
        doc[F("dateTime")] = buffer;
    }

    JsonObject jwifi = doc[F("wifi")].to<JsonObject>();
    jwifi[F("status")] =  WiFi.status();
    jwifi[F("mode")] = WiFi.getMode();
    jwifi[F("ipsta")] = WiFi.localIP().toString();
    jwifi[F("mac")] = WiFi.macAddress();
    jwifi[F("hostname")] = WiFi.getHostname();
    jwifi[F("sta_ssid")] = WiFi.SSID();
    jwifi[F("rssi")] = WiFi.RSSI();
    
    JsonObject jmqtt = doc[F("mqtt")].to<JsonObject>();
    jmqtt[F("connected")] = mqtt.connected();
    jmqtt[F("basetopic")] = mqtt.getBaseTopic();
    jmqtt[F("numDisc")] = mqtt.getNumDisc();

    otcontrol.getJson(doc);

    outsideTemp.writeJson(doc[F("outsideTemp")].to<JsonVariant>());

    if (!outsideTemp.owResult.isEmpty())
        doc[F("owResult")] = outsideTemp.owResult;

    JsonObject jo = doc[F("1wire")].to<JsonObject>();
    OneWireNode::writeJsonAll(jo);

    JsonObject ble = doc[F("BLE")].to<JsonObject>();
    BLESensor::writeJsonAll(ble);

    for (int i=0; i<sizeof(auxInput) / sizeof(auxInput[0]); i++)
        auxInput[i].getJson(doc);
}
