arrys/OT-Thing/Firmware/include/devconfig.h

#ifndef _devconfig_h
#define _devconfig_h

#include <Arduino.h>
#include <ArduinoJson.h>
#include <LittleFS.h>

extern class DevConfig {
private:
    bool update();
    bool writeBufFlag;
    String hostname;
    int timezone;
    bool authConfigured;
    String authSalt;
    String authHash;
public:
    DevConfig();
    bool begin();
    File getFile();
    void write(String &str);
    void remove();
    void loop();
    bool isAuthConfigured() const;
    bool verifyUiCredentials(const String &password) const;
    bool setUiCredentials(const String &password);
    bool clearUiCredentials();
    String getHostname() const;
    int getTimezone() const;
    bool masterOvrdEnabled; // set if otMode is master/test and slave is enabled
} devconfig;

extern const char CFG_FILENAME[] PROGMEM;

extern PGM_P STR_CONFKEY_HYSTERESIS PROGMEM;
extern PGM_P STR_CONFKEY_HEATING PROGMEM;
extern PGM_P STR_CONFKEY_RETURNLIMIT PROGMEM;

#endif
