arrys/OT-Thing/Firmware/include/devstatus.h

#ifndef _devstatus_h
#define _devstatus_h

#include <Arduino.h>
#include <ArduinoJson.h>
#include <ESPAsyncWebServer.h>
#include "util.h"

extern PGM_P STR_STATKEY_MASTER PROGMEM;
extern PGM_P STR_STATKEY_SLAVE PROGMEM;
extern PGM_P STR_STATKEY_ROOMUNIT PROGMEM;
extern PGM_P STR_STATKEY_ROOMCOMPINTEGRATOR PROGMEM;
extern PGM_P STR_STATKEY_ROOMTEMP PROGMEM;
extern PGM_P STR_STATKEY_ROOMSETPOINT PROGMEM;
extern PGM_P STR_STATKEY_CTRLMODE PROGMEM;
extern PGM_P STR_STATKEY_FLOWMIN PROGMEM;
extern PGM_P STR_STATKEY_OVERRIDE_TEMP PROGMEM;
extern PGM_P STR_STATKEY_OVERRIDE_ON PROGMEM;
extern PGM_P STR_STATKEY_OVERRIDE PROGMEM;
extern PGM_P STR_STATKEY_ACTION PROGMEM;
extern PGM_P STR_STATKEY_DHW PROGMEM;
extern PGM_P STR_STATKEY_VENT PROGMEM;
extern PGM_P STR_STATKEY_SETPOINT PROGMEM;
extern PGM_P STR_STATKEY_RETURNLIMITINTEGRATOR PROGMEM;
extern PGM_P STR_STATKEY_ROOMACTION PROGMEM;
extern PGM_P STR_STATKEY_ROOMMODE PROGMEM;
extern PGM_P STR_STATKEY_SUSPENDED PROGMEM;
extern PGM_P STR_STATKEY_SUMMERMODE PROGMEM;
extern PGM_P STR_STATKEY_DHWBLOCKING PROGMEM;
extern PGM_P STR_STATKEY_ENABLE PROGMEM;
extern PGM_P STR_STATKEY_OPENBYPASS PROGMEM;
extern PGM_P STR_STATKEY_AUTOBYPASS PROGMEM;
extern PGM_P STR_STATKEY_FREEVENTENABLE PROGMEM;
extern PGM_P STR_STATKEY_LASTSETPOINTSRC PROGMEM;
extern PGM_P STR_STATKEY_BYPASS PROGMEM;
extern PGM_P STR_STATKEY_TXCOUNT PROGMEM;
extern PGM_P STR_STATKEY_RXCOUNT PROGMEM;

extern PGM_P STR_STATKEY_FLAMESTATS PROGMEM;
extern PGM_P STR_STATKEY_FLAMESTATS_DUTY PROGMEM;
extern PGM_P STR_STATKEY_FLAMESTATS_FREQ PROGMEM;
extern PGM_P STR_STATKEY_FLAMESTATS_ONTIME PROGMEM;
extern PGM_P STR_STATKEY_FLAMESTATS_OFFTIME PROGMEM;
extern PGM_P STR_STATKEY_FLAMESTATS_CURRENTONTIME PROGMEM;
extern PGM_P STR_STATKEY_FLAMESTATS_LASTONTIME PROGMEM;
extern PGM_P STR_STATKEY_FLOWSET_TEMP PROGMEM;
extern PGM_P STR_STATKEY_COOLING PROGMEM;
extern PGM_P STR_STATKEY_FLOWSETPOINT PROGMEM;

extern class DevStatus {
friend class DevStatusLock;
private:
    SemaphoreHandle_t mutex;
public:
    DevStatus();
    bool lock();
    void unlock();
    void buildDoc(JsonObject doc);
    uint32_t numWifiDiscon;
} devstatus;

#endif
