arrys/OT-Thing/Firmware/tools/production.py

#!/usr/bin/env python3
# /// script
# requires-python = ">=3.10"
# dependencies = [
#     "esptool>=5,<6",
#     "pyserial>=3.5",
#     "requests>=2.31",
#     "platformio>=6.1,<7",
# ]
# ///

"""
Production batch firmware upload script for OTthing devices.

Run with `uv run Firmware/tools/production.py` from the repository root.

Handles:
- Stable USB device detection (VID/PID)
- Bootloader, firmware, and partitions upload
- Device configuration (MAC reading, hard reset, network setup)
- Batch mode with continuous device reprogramming
"""

import os
import sys
import socket
import subprocess
import time
import webbrowser
import shutil
import winsound
import serial
from pathlib import Path

# ANSI colour output
if sys.platform == "win32":
    os.system("")  # enable VT processing on Windows
_RED    = "\033[91m"
_GREEN  = "\033[92m"
_YELLOW = "\033[93m"
_CYAN   = "\033[96m"
_RESET  = "\033[0m"

def _ok(msg):   print(f"{_GREEN}{msg}{_RESET}")
def _err(msg):  print(f"{_RED}{msg}{_RESET}")
def _warn(msg): print(f"{_YELLOW}{msg}{_RESET}")
def _act(msg):  print(f"{_CYAN}{msg}{_RESET}")


def _release_artifact_paths(project_dir):
    """Return expected release binary paths."""
    build_dir = os.path.join(project_dir, ".pio", "build", "release")
    return {
        "bootloader": os.path.join(build_dir, "bootloader.bin"),
        "partitions": os.path.join(build_dir, "partitions.bin"),
        "firmware": os.path.join(build_dir, "firmware.bin"),
    }


def _parse_partition_size(value):
    """Parse a partitions.csv offset/size field (hex, or K/M suffixed) into bytes."""
    value = value.strip()
    if value.lower().startswith("0x"):
        return int(value, 16)
    if value[-1:].upper() == "K":
        return int(value[:-1]) * 1024
    if value[-1:].upper() == "M":
        return int(value[:-1]) * 1024 * 1024
    return int(value)


def _read_partition_table(project_dir):
    """Parse partitions.csv into {name: (offset, size)} in bytes."""
    csv_path = os.path.join(project_dir, "partitions.csv")
    partitions = {}
    with open(csv_path, "r", encoding="utf-8") as f:
        for line in f:
            line = line.strip()
            if not line or line.startswith("#"):
                continue
            fields = [p.strip() for p in line.split(",")]
            if len(fields) < 5:
                continue
            name, _ptype, _subtype, offset_str, size_str = fields[:5]
            partitions[name] = (_parse_partition_size(offset_str), _parse_partition_size(size_str))
    return partitions


def _find_platformio_executable(project_dir):
    """Resolve a usable PlatformIO CLI executable."""
    candidates = [
        shutil.which("platformio"),
        shutil.which("pio"),
    ]

    home = os.path.expanduser("~")
    candidates.append(os.path.join(home, ".platformio", "penv", "Scripts", "platformio.exe"))
    candidates.append(os.path.join(home, ".platformio", "penv", "bin", "platformio"))

    workspace_penv = os.path.join(project_dir, ".venv", "Scripts", "platformio.exe")
    candidates.append(workspace_penv)

    for candidate in candidates:
        if candidate and os.path.exists(candidate):
            return candidate
    return None


def newest_source_mtime(project_dir):
    """Newest mtime across the inputs that affect a release firmware image."""
    roots = ["src", "include", "lib", "data"]
    files = ["platformio.ini", "partitions.csv", "helper.py", "default.ini"]
    newest = 0.0
    for root in roots:
        base = os.path.join(project_dir, root)
        for dirpath, _dirnames, filenames in os.walk(base):
            for name in filenames:
                # helper.py writes include/html.h, which must not count as input.
                if name == "html.h":
                    continue
                newest = max(newest, os.path.getmtime(os.path.join(dirpath, name)))
    for name in files:
        path = os.path.join(project_dir, name)
        if os.path.exists(path):
            newest = max(newest, os.path.getmtime(path))
    return newest


def ensure_release_build(project_dir):
    """Build release firmware if artifacts are missing or older than the sources."""
    artifacts = _release_artifact_paths(project_dir)
    missing = [path for path in artifacts.values() if not os.path.exists(path)]
    if not missing:
        # Existence alone is not enough: flashing an artifact built from an
        # earlier commit would ship the wrong firmware.
        newest_src = newest_source_mtime(project_dir)
        oldest_artifact = min(os.path.getmtime(p) for p in artifacts.values())
        if newest_src and oldest_artifact < newest_src:
            _warn("Release build artifacts are older than the sources - rebuilding.")
            missing = list(artifacts.values())
        else:
            return True

    _warn("Release build artifacts missing. Starting `platformio run --environment release`...")
    pio = _find_platformio_executable(project_dir)
    if not pio:
        _err("✗ PlatformIO executable not found. Install PlatformIO or add it to PATH.")
        return False

    result = subprocess.run([pio, "run", "--environment", "release"], cwd=project_dir)
    if result.returncode != 0:
        _err("✗ Release build failed.")
        return False

    missing_after = [path for path in artifacts.values() if not os.path.exists(path)]
    if missing_after:
        _err("✗ Release build finished but artifacts are still missing:")
        for path in missing_after:
            print(f"  {path}")
        return False

    _ok("✓ Release build completed")
    return True

# USB Device IDs
TARGET_USB_VID = 0x303A
TARGET_USB_PID = 0x1001
STABLE_DEVICE_SECONDS = 4.0
DEVICE_POLL_INTERVAL_SECONDS = 0.5

# Fixed bootloader / partition table offsets (ESP32-C3 image format).
BOOTLOADER_OFFSET = 0x0
PARTITION_TABLE_OFFSET = 0x8000
EXPECTED_CHIP = "ESP32-C3"


def parse_partition_offsets(csv_path):
    """Return (offset, size) of the ota_0 app partition from partitions.csv.

    The firmware offset used to be hardcoded as 0x10000, which silently drifts
    out of sync if the nvs/otadata sizes above app0 are ever changed. Sizes may
    be given as plain bytes or with a K/M suffix.
    """
    for raw in Path(csv_path).read_text(encoding="utf-8").splitlines():
        line = raw.strip()
        if not line or line.startswith("#"):
            continue
        cols = [c.strip() for c in line.split(",")]
        # Name, Type, SubType, Offset, Size, Flags
        if len(cols) < 5 or cols[1] != "app":
            continue
        if cols[2] != "ota_0":
            continue

        def to_bytes(txt):
            txt = txt.strip().upper()
            mult = 1
            if txt.endswith("K"):
                mult, txt = 1024, txt[:-1]
            elif txt.endswith("M"):
                mult, txt = 1024 * 1024, txt[:-1]
            return int(txt, 0) * mult

        return to_bytes(cols[3]), to_bytes(cols[4])
    raise ValueError(f"no ota_0 app partition found in {csv_path}")


def verify_flash_result(result):
    """True only if write_flash() reported a successful verify for every segment."""
    if not isinstance(result, dict):
        # No verifiable report: treat as failure rather than silently succeeding.
        return False
    verify = result.get("verify")
    if isinstance(verify, dict):
        return bool(verify) and all(v is True for v in verify.values())
    return False

# Device Network Configuration
DEVICE_IP = "4.3.2.1"
DEVICE_DATA_PORT = 25238

# Default OTthing configuration
CONFIG = {
    "slaveApp": 0,  # heat/cool
    "otMode": 1,  # master
    "enableSlave": False,
    "otDelay": 100,
    "noDhwSet": False,
    "boiler": {
        "dhwOn": True,
        "dhwTemperature": 50,
        "dhwSchedule": {"enabled": False, "entries": []},
        "dhwCtrlSource": 2,
        "overrideDhw": False,
        "coolOn": False,
        "maxModulation": 100,
        "otc": False,
        "summerMode": False,
        "dhwBlocking": False,
        "chOffTemp": 10,
        "texhaustAsFloat": False,
    },
    "heating": [
        {
            "flow": 45,
            "chOn": True,
            "flowMax": 60,
            "flowMin": 10,
            "exponent": 1.3,
            "gradient": 1.0,
            "offset": 0,
            "marker": [],
            "schedule": {"enabled": False, "entries": []},
            "roomsetpoint": {"source": 0, "temp": 21},
            "roomtemp": {"source": 1},
            "overrideFlow": False,
            "overrideOn": False,
            "roomComp": {"enabled": False, "p": 1.0, "i": 0.5, "boost": 1.0},
            "enableHyst": False,
            "hysteresis": 0.5,
            "curveMode": 0,
            "minSuspend": False,
            "minSuspHyst": 0.2,
            "suspOffset": 0.0,
            "outsideSuspend": {
                "type": 1,
                "hysteresis": 0.2,
                "offset": 0.0
            },
            "returnLimit": {
                "source": 1,
                "deltaT": 0.0
            }
        },
        {
            "flow": 30,
            "chOn": False,
            "flowMax": 40,
            "flowMin": 10,
            "exponent": 1.3,
            "gradient": 1.0,
            "offset": 0,
            "marker": [],
            "schedule": {"enabled": False, "entries": []},
            "roomsetpoint": {"source": 0, "temp": 21},
            "roomtemp": {"source": 1},
            "overrideFlow": False,
"overrideOn": False,
            "roomComp": {"enabled": False, "p": 1.0, "i": 0.0, "boost": 1.0},
            "enableHyst": False,
            "hysteresis": 0.5,
            "curveMode": 0,
            "minSuspend": False,
            "minSuspHyst": 0.2,
            "suspOffset": 0.0,
            "outsideSuspend": {
                "type": 1,
                "hysteresis": 0.2,
                "offset": 0.0
            },
            "returnLimit": {
                "source": 1,
                "deltaT": 0.0
            }
        },
    ],
    "vent": {
        "ventEnable": False,
        "openBypass": False,
        "autoBypass": False,
        "freeVentEnable": False,
        "setpoint": 3,
    },
    # Outside temp disabled (source 0) by default: enable it and set your own
    # coordinates/apikey per unit rather than shipping a fixed location.
    "outsideTemp": {"source": 0, "apikey": None, "lat": 0.0, "lon": 0.0, "interval": 300},
    "mqtt": {"host": "", "port": 1883, "user": "", "pass": "", "tls": False, "keepAlive": 15},
    "masterMemberId": 8,
    "timezone": 3600,
    "hostname": "otthing",
    "haPrefix": "homeassistant",
    "aux": [{"mode": 4, "digitalRole": 0}, {"mode": 0, "digitalRole": 0}],  # DQ: 1wire, DI: not used
}

def get_target_port():
    """Find the OTthing device on USB by VID/PID."""
    from serial.tools import list_ports

    for d in list_ports.comports():
        if (d.vid == TARGET_USB_VID) and (d.pid == TARGET_USB_PID):
            return d.device
    return None


def wait_for_stable_target_port(stable_seconds=STABLE_DEVICE_SECONDS):
    """
    Wait for the USB device to appear and stay continuously present.

    A USB device commonly enumerates before its USB-CDC serial interface is
    usable, so returning on first sight races the port opening. The port name is
    returned only after it has been present for the whole settle window.
    """
    last_port = None
    appeared_at = None

    _act(
        f"Waiting for USB device VID:PID {TARGET_USB_VID:04X}:{TARGET_USB_PID:04X}... (Ctrl+C to stop)"
    )

    while True:
        port = get_target_port()

        if port is None:
            if last_port is not None:
                _act("Device disappeared, waiting for it to re-appear...")
            last_port = None
            appeared_at = None
            time.sleep(DEVICE_POLL_INTERVAL_SECONDS)
            continue

        now = time.time()
        if port != last_port:
            # A different port (or the same one re-enumerating) restarts the window.
            last_port = port
            appeared_at = now
            time.sleep(DEVICE_POLL_INTERVAL_SECONDS)
            continue

        if appeared_at is not None and (now - appeared_at) >= stable_seconds:
            _act(f"Device {port} stable for {stable_seconds:g}s. Starting upload.")
            return port

        time.sleep(DEVICE_POLL_INTERVAL_SECONDS)


def upload_firmware(port, project_dir):
    """
    Upload bootloader, firmware, and partitions to device using esptool.
    Reads chip info (type, MAC) before programming and returns it.

    Assumes firmware has already been built in .pio/build/release/

    Args:
        port: Serial port (e.g., 'COM3')
        project_dir: Project directory containing .pio/build/release/

    Returns:
        dict with keys 'chip', 'mac' on success, or None on failure.
    """
    # Paths to build artifacts
    artifacts = _release_artifact_paths(project_dir)
    bootloader_path = artifacts["bootloader"]
    partition_path = artifacts["partitions"]
    firmware_path = artifacts["firmware"]

    # Check if all binaries exist
    if not all(os.path.exists(p) for p in [bootloader_path, partition_path, firmware_path]):
        if not ensure_release_build(project_dir):
            _err("✗ Build artifacts not found at:")
            print(f"  {bootloader_path}")
            print(f"  {partition_path}")
            print(f"  {firmware_path}")
            print("\nRun: pio run -e release")
            return None

    # Resolve the app offset from partitions.csv instead of hardcoding it.
    partitions_csv = os.path.join(project_dir, "partitions.csv")
    try:
        app_offset, app_size = parse_partition_offsets(partitions_csv)
    except (OSError, ValueError) as exc:
        _err(f"✗ Cannot determine app offset: {exc}")
        return None

    fw_size = os.path.getsize(firmware_path)
    if fw_size > app_size:
        _err(
            f"✗ firmware.bin is {fw_size} bytes but the ota_0 partition is only "
            f"{app_size} bytes (offset 0x{app_offset:X})"
        )
        return None

    print(f"\n=== Uploading firmware to {port} ===")

    try:
        import esptool

        esp = None
        try:
            esp = esptool.cmds.detect_chip(port=port)
            esp = esp.run_stub()
            chip_desc = esp.get_chip_description()
            mac = ":".join(f"{b:02x}" for b in esp.read_mac("BASE_MAC"))
            print(f"Chip : {chip_desc}")
            print(f"MAC  : {mac}")

# VID:PID 303A:1001 matches every Espressif native-USB part, so a
            # S2/S3 would happily accept a C3 bootloader at fixed offsets.
            if EXPECTED_CHIP not in chip_desc:
                raise RuntimeError(
                    f"expected {EXPECTED_CHIP}, found '{chip_desc}' - refusing to flash"
                )

            # Erase only NVS and LittleFS partitions so old config/data can't survive
            # reprogramming, while leaving the app and otadata partitions intact.
            partitions = _read_partition_table(project_dir)
            for part_name in ("nvs", "spiffs"):
                if part_name in partitions:
                    offset, size = partitions[part_name]
                    print(f"Erasing '{part_name}' partition (offset=0x{offset:x}, size={size} bytes)...")
                    esptool.cmds.erase_region(esp, offset, size)
                else:
                    _warn(f"⚠ Partition '{part_name}' not found in partitions.csv, skipping erase")

            print("Writing bootloader, partition table, and firmware...")
            result = esptool.cmds.write_flash(
                esp,
                [
                    (BOOTLOADER_OFFSET, bootloader_path),
                    (PARTITION_TABLE_OFFSET, partition_path),
                    (app_offset, firmware_path),
                ],
            )
            # write_flash returns per-segment MD5 verify results. A failed or
            # skipped verify means the flash content is unknown, so do not
            # report success.
            if not verify_flash_result(result):
                raise RuntimeError(
                    "flash verification failed: "
                    + str(result.get("verify") if isinstance(result, dict) else result)
                )
            _ok("✓ Firmware uploaded successfully")
        finally:
            # _port is a private esptool attribute and may be absent.
            close = getattr(getattr(esp, "_port", None), "close", None)
            if close is not None:
                close()

        return {"chip": chip_desc, "mac": mac}
    except Exception as e:
        _err(f"✗ Upload failed: {e}")
        _warn("Restarting programming cycle from device detection...")
        return None


def verify_tcp_stream(host, port, max_cycles=20, connect_timeout=30, read_timeout=10):
    """Connect to a TCP/IP port and verify a well-formed OT event stream.

    Only the per-line format is checked. The device emits interleaved frames
    depending on mode and on what is attached to the slave port: in master mode
    (what this tool configures) only T/B/A/E appear, and the room-unit frames
    S/P/R only show up when a unit is actually polling the slave port. The
    previous fixed T→S→P→B cycle could therefore never be satisfied on a
    freshly flashed device.
    """
    import re

    # T=master req to boiler, B/A=boiler response (as-is/rewritten), E=invalid
    # frame, S=room unit request, P=response to room unit, R=repeater rewrite.
    line_pattern = re.compile(r"^[TSPBAREtspbare][0-9A-Fa-f]{8}$")
    min_lines = max_cycles
    print(f"\n=== Verifying TCP/IP stream on {host}:{port} ({max_cycles} cycles) ===")

    deadline = time.time() + connect_timeout
    sock = None
    while time.time() < deadline:
        try:
            sock = socket.create_connection((host, port), timeout=connect_timeout)
            break
        except OSError as exc:
            print(f"Waiting for TCP/IP port {host}:{port}... ({exc})")
            time.sleep(1)

    if sock is None:
        _err(f"✗ Could not connect to {host}:{port} within {connect_timeout}s")
        return False

    with sock:
        sock.settimeout(read_timeout)
        try:
            with sock.makefile("r", encoding="utf-8", newline="\n") as stream:
                lines_read = 0
                for _ in range(max_lines):
                    line = stream.readline()
                    if not line:
                        break
                    line = line.strip()
                    if not line:
                        continue
                    lines_read += 1
                    print(f"TCP[{lines_read}]: {line}")
                    if not line_pattern.match(line):
                        _err(f"✗ Invalid line format: '{line}'. Expected a source letter + 8 hex digits.")
                        return False

                if lines_read < min_lines:
                    _err(f"✗ Only received {lines_read}/{min_lines} lines.")
                    return False

        except OSError as exc:
            _err(f"✗ TCP/IP read failed: {exc}")
            return False

    _ok("✓ TCP/IP stream verified")
    return True


def verify_http_page(host, port=80, connect_timeout=30, read_timeout=40):
    """Open an HTTP connection and verify a valid HTML page is returned."""
    print(f"\n=== Verifying HTTP page on http://{host}:{port}/ ===")
    deadline = time.time() + connect_timeout

    while time.time() < deadline:
        try:
            with socket.create_connection((host, port), timeout=connect_timeout) as sock:
                sock.settimeout(read_timeout)
                request = (
                    f"GET / HTTP/1.0\r\n"
                    f"Host: {host}\r\n"
                    "Connection: close\r\n"
                    "\r\n"
                )
                sock.sendall(request.encode("ascii"))

                # Read the full response until connection closes
                response = b""
                while True:
                    try:
                        chunk = sock.recv(4096)
                    except OSError:
                        break
                    if not chunk:
                        break
                    response += chunk

                content = response.decode("utf-8", errors="replace")
                if "HTTP/" not in content:
                    _err("✗ Invalid HTTP response")
                    return False

                status_line = content.splitlines()[0] if content.splitlines() else ""
                print(f"HTTP status: {status_line}")
                if "200" not in status_line:
                    _err("✗ Non-OK HTTP status")
                    return False

                body_start = response.find(b"\r\n\r\n")
                headers = response[:body_start].decode("utf-8", errors="replace") if body_start >= 0 else ""
                body = response[body_start + 4:] if body_start >= 0 else b""

                print(f"Body size: {len(body)} bytes, headers: {headers[:200].strip()}")

                if not body:
                    _err("✗ Response body is empty")
                    return False

                # Handle gzip-encoded response — detect by magic bytes since ESP32
                # often omits Content-Encoding: gzip header
                is_gzip = ("content-encoding: gzip" in headers.lower()) or body[:2] == b"\x1f\x8b"
                if is_gzip:
                    import gzip
                    try:
                        body = gzip.decompress(body)
                    except Exception as exc:
                        _err(f"✗ Failed to decompress gzip body: {exc}")
                        return False

                if b"<html" not in body.lower() and b"<!doctype" not in body.lower():
                    _err("✗ Response body does not contain valid HTML")
                    return False

                _ok("✓ HTTP page verified")
                return True
        except OSError as exc:
            print(f"Waiting for HTTP port {host}:{port}... ({exc})")
            time.sleep(1)

    _err(f"✗ Could not connect to HTTP server on {host}:{port} within {connect_timeout}s")
    return False


def _parse_wifi_interfaces(output):
    """Split `netsh wlan show interfaces` output into per-interface field dicts."""
    interfaces = []
    current = {}
    for raw_line in output.splitlines():
        line = raw_line.strip()
        if not line:
            if current:
                interfaces.append(current)
                current = {}
            continue
        if ":" in line:
            key, _, value = line.partition(":")
            key = key.strip()
            value = value.strip()
            if key == "Name":
                if current:
                    interfaces.append(current)
                current = {"Name": value}
            elif current:
                current[key] = value
    if current:
        interfaces.append(current)
    return interfaces


def _query_netsh_wlan_status():
    """Return list of WiFi interface field dicts as reported by netsh (SSID/status).

    Note: netsh can silently omit data for some adapters when Windows Location
    Services are disabled, so this must not be used to enumerate interfaces.
    """
    result = subprocess.run(
        ["netsh", "wlan", "show", "interfaces"],
        capture_output=True, text=True, encoding="cp850", errors="replace"
    )
    return _parse_wifi_interfaces(result.stdout)


def list_wifi_interfaces():
    """Return list of WiFi adapter names via PowerShell (unaffected by netsh's
    Location-Services dependent output, which can silently hide adapters)."""
    ps_cmd = (
        "Get-NetAdapter | Where-Object { $_.PhysicalMediaType -like '*802.11*' "
        "-or $_.MediaType -like '*802.11*' } | Select-Object -ExpandProperty Name"
    )
    result = subprocess.run(
        ["powershell", "-NoProfile", "-Command", ps_cmd],
        capture_output=True, text=True
    )
    return [{"Name": name.strip()} for name in result.stdout.splitlines() if name.strip()]


def prompt_wifi_interface():
    """If multiple WiFi interfaces exist, ask the user which one to use."""
    names = [i.get("Name") for i in list_wifi_interfaces() if i.get("Name")]
    if len(names) <= 1:
        return names[0] if names else None

    print("Multiple WiFi interfaces detected:")
    for idx, name in enumerate(names, 1):
        print(f"  {idx}. {name}")
    while True:
        choice = input(f"Select interface to use [1-{len(names)}]: ").strip()
        if choice.isdigit() and 1 <= int(choice) <= len(names):
            return names[int(choice) - 1]
        print("Invalid selection, try again.")

def disconnect_wifi(profile="OTthing", interface=None):
    target = f" on interface {interface}" if interface else ""
    print(f"Disconnecting from WiFi (profile: {profile}){target}...")
    argv = ["netsh", "wlan", "disconnect"]
    if interface:
        argv += ["interface", interface]
    result = subprocess.run(argv, capture_output=True, text=True)
    if result.stdout.strip():
        print(result.stdout.strip())
    if result.returncode != 0:
        print(result.stderr.strip())
        return False
    return True

def connect_to_otthing_wifi(profile="OTthing", timeout=20, retries=3, interface=None):
    if sys.platform != "win32":
        _warn("WiFi connect needs netsh, which is Windows-only. Skipping.")
        return False

    def _netsh_connect():
        target = f" on interface {interface}" if interface else ""
        print(f"Connecting to OTthing WiFi (profile: {profile}){target}...")
        # Argument vector, not a cmd.exe string: profile and interface are
        # operator-supplied and would otherwise be parsed for &, | and %
        # metacharacters.
        argv = ["netsh", "wlan", "connect", "name", profile]
        if interface:
            argv += ["interface", interface]
        result = subprocess.run(argv, capture_output=True, text=True)
        if result.stdout.strip():
            print(result.stdout.strip())
        if result.returncode != 0:
            print(result.stderr.strip())
            return False
        return True

    for attempt in range(1, retries + 1):
        if not _netsh_connect():
            return False

        wait = 8 if attempt == 1 else 5
        disconnected_early = False
        for remaining in range(wait, 0, -1):
# Query current WiFi SSID every second during the wait, scoped to the selected interface
            all_interfaces = _query_netsh_wlan_status()
            if interface:
                selected = next((i for i in all_interfaces if i.get("Name") == interface), None)
                check_lines = [f"{k}                   : {v}" for k, v in selected.items()] if selected else []
            else:
                check_lines = subprocess.run(
                    ["netsh", "wlan", "show", "interfaces"],
                    capture_output=True, text=True, encoding="cp850", errors="replace"
                ).stdout.splitlines()
            ssid_line = next((l.strip() for l in check_lines if "SSID" in l and "BSSID" not in l), "SSID: ?")
            state_line = next((l.strip() for l in check_lines if "Status" in l), "State: ?")
            print(f"  [{remaining:2d}s] {state_line} | {ssid_line}")
            output_lower = "\n".join(check_lines).lower()
            # Break early if already associated
            if ("verbunden" in output_lower or "connected" in output_lower) and profile.lower() in output_lower:
                print(f"  WiFi associated after {wait - remaining + 1}s")
                break
            if "verbindung wird getrennt" in output_lower:
                time.sleep(1)
                continue
            # If fully disconnected (not just associating), retry connect immediately
            if "getrennt" in output_lower or "disconnected" in output_lower:
                _warn("  Disconnected — retrying netsh connect immediately...")
                disconnected_early = True
                break
            time.sleep(1)

        if disconnected_early:
            continue  # skip IP probe, go straight to next netsh connect attempt

        # Probe the device IP to confirm the WiFi link is up
        deadline = time.time() + timeout
        connected = False
        while time.time() < deadline:
            try:
                with socket.create_connection((DEVICE_IP, 80), timeout=5):
                    _ok(f"✓ Connected to WiFi profile {profile} (device reachable at {DEVICE_IP})")
                    connected = True
                    break
            except OSError:
                time.sleep(1)

        if connected:
            return True

        _warn(f"⚠ Device not reachable at {DEVICE_IP} after attempt {attempt}/{retries}, retrying netsh...")

    _err(f"✗ OTthing WiFi did not become connected after {retries} attempt(s)")
    return False


def configure_device():
    """
    Configure device after firmware upload.
    Uses DEVICE_IP for web interface connection.

    Returns:
        bool: True on success, False on failure.
    """
    print(f"\n=== Configuring device ===")
    
    # Send configuration
    try:
        import requests
    except ImportError:
        _err("✗ 'requests' is not installed. Run: pip install requests")
        return False

    try:
        config_endpoint = f"http://{DEVICE_IP}/config"
        print(f"Sending config to {config_endpoint}...")
        response = requests.post(config_endpoint, json=CONFIG, timeout=5)
        print(f"Response: {response.status_code}")
        
        # Verify configuration
        time.sleep(1)
        response = requests.get(config_endpoint, timeout=3)
        conf = response.json()
        
        # Compare sent vs received
        import json
        if conf == CONFIG:
            _ok("✓ Configuration verified - device matches sent config")
        else:
            _warn("⚠ Configuration mismatch detected:")
            print("Sent:")
            print(json.dumps(CONFIG, indent=2))
            print("\nReceived:")
            print(json.dumps(conf, indent=2))
        
        _ok("✓ Device configured successfully")
        return True
    except Exception as e:
        _err(f"✗ Configuration failed: {e}")
        return False


def wait_for_device_disconnect():
    """
    Wait for the USB device to be disconnected.
    """
    _act("Waiting for device to disconnect...")
    
    while True:
        port = get_target_port()
        if port is None:
            _ok("✓ Device disconnected")
            return
        time.sleep(DEVICE_POLL_INTERVAL_SECONDS)


def _get_firmware_version(project_dir):
    """Read custom_version from platformio.ini."""
    ini_path = os.path.join(project_dir, "platformio.ini")
    try:
        import configparser
        cfg = configparser.ConfigParser()
        cfg.read(ini_path)
        return cfg.get("env", "custom_version", fallback="unknown").strip()
    except Exception:
        return "unknown"


def _log_device(project_dir, device_info):
    """Append one-line device entry to devicelist.txt if MAC is not already present."""
    import datetime
    import re

    mac = device_info["mac"].lower()
    version = _get_firmware_version(project_dir)
    timestamp = datetime.datetime.now().strftime("%Y-%m-%d %H:%M:%S")
    line = (
        f"{timestamp}  "
        f"chip={device_info['chip']}  "
        f"mac={mac}  "
        f"fw={version}\n"
    )
    log_path = os.path.join(project_dir, "devicelist.txt")

    # Skip duplicate MAC entries while still allowing the file to be created.
    if os.path.exists(log_path):
        with open(log_path, "r", encoding="utf-8", errors="replace") as f:
            existing = f.read().lower()
        existing_macs = set(re.findall(r"\bmac=([0-9a-f]{2}(?::[0-9a-f]{2}){5})\b", existing))
        if mac in existing_macs:
            _warn(f"⚠ MAC already present in devicelist.txt, skipping log entry: {mac}")
            return

    with open(log_path, "a", encoding="utf-8") as f:
        f.write(line)
    _ok(f"✓ Logged to devicelist.txt: {line.strip()}")


def batch_upload(project_dir):
    """
    Continuous batch upload loop.
    
    Detects stable USB connections and uploads firmware to each device.
    Press Ctrl+C to stop.
    """
    print("\n=== Batch firmware upload mode ===")
    _act("Connect devices one at a time. Each will be programmed automatically.\n")

    # Open the device web UI once at startup; keep reusing the same tab/window.
    config_url = f"http://{DEVICE_IP}"
    print(f"Opening {config_url} (once at startup)...")
    webbrowser.open(config_url)

    wifi_interface = prompt_wifi_interface()

    upload_count = 0
    failure_count = 0
    
    while True:
        try:
            stable_port = wait_for_stable_target_port()
        except KeyboardInterrupt:
            print(f"\n\nBatch mode stopped. Programmed {upload_count} device(s), {failure_count} failure(s).")
            break

        disconnect_wifi(interface=wifi_interface)
        # Upload firmware
        device_info = upload_firmware(stable_port, project_dir)
        if device_info:
            upload_count += 1

            # resset device by toggling DTR
            with serial.Serial(stable_port) as port:
                time.sleep(.20)

            time.sleep(2)

            if not connect_to_otthing_wifi(interface=wifi_interface):
                failure_count += 1
            elif not verify_tcp_stream(DEVICE_IP, DEVICE_DATA_PORT):
                failure_count += 1
            elif not verify_http_page(DEVICE_IP, 80):
                failure_count += 1
            else:
                # Attempt configuration
                if not configure_device():
                    failure_count += 1
                else:
                    # Log device info
                    _log_device(project_dir, device_info)
                    _ok("\n" + "=" * 50)
                    _ok(f"  ✓  DEVICE #{upload_count} COMPLETE — ALL STEPS PASSED")
                    _ok("=" * 50 + "\n")
                    winsound.Beep(800, 100)
                    winsound.Beep(1200, 100)
                    winsound.Beep(1600, 100)
        else:
            failure_count += 1
            time.sleep(1)
            continue
        
        # Wait for next device
        _act("Connect the next one...")
        wait_for_device_disconnect()
        time.sleep(1)


if __name__ == "__main__":
    import os
    
    # Script lives in tools/, so project root is one level up.
    project_dir = os.path.dirname(os.path.dirname(os.path.abspath(__file__)))
    
    try:
        batch_upload(project_dir)
    except KeyboardInterrupt:
        print("\nBatch upload cancelled.")
